skuep/EZ-Dipole/kicad/ez-dipole/ez-dipole.kicad_sch

## KiCad design kicad/ez-dipole/ez-dipole.kicad_sch (2023-12-30, an earlier design)

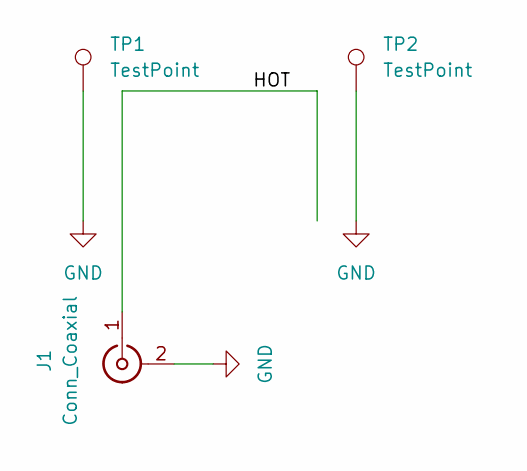
[picture p7: schematic ez-dipole.kicad_sch]

Parts:
J1: Conn_Coaxial; SMA_Amphenol_132289_EdgeMount
TP1, TP2: TestPoint; Slot

Connections:
GND: J1.2 (Ext), TP1.1, TP2.1
HOT: J1.1 (In)
